Nizam704/Self-Guided-Projectile-Bot/Project parts/Solidworks parts/Part3.SLDPRT

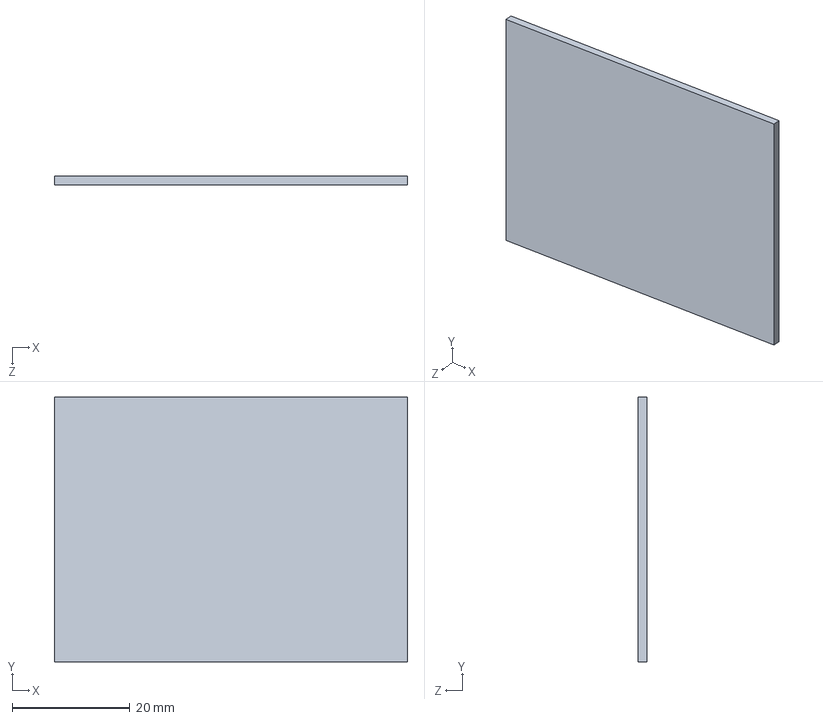
[picture p39: CAD file, 2025-05-20]
Project parts/Solidworks parts/Part3.SLDPRT
60.0 x 45.0 x 1.50 mm
