Nizam704/Self-Guided-Projectile-Bot/Project parts/Cura files/stand holder.STL

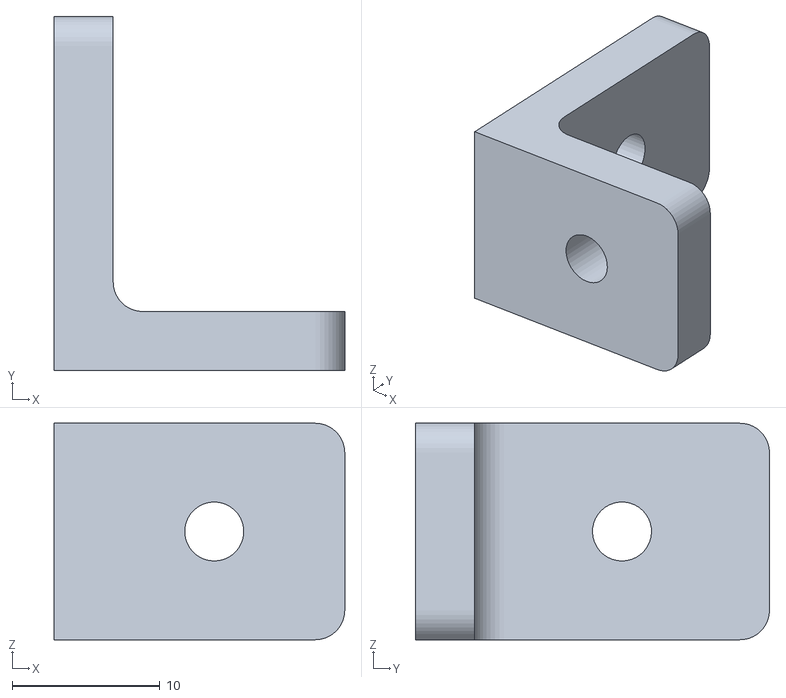
[picture p40: CAD file, 2025-05-20]
Project parts/Cura files/stand holder.STL
19.7 x 24.0 x 14.7
