Nizam704/Self-Guided-Projectile-Bot/Project parts/Cura files/ball holder preview.STL

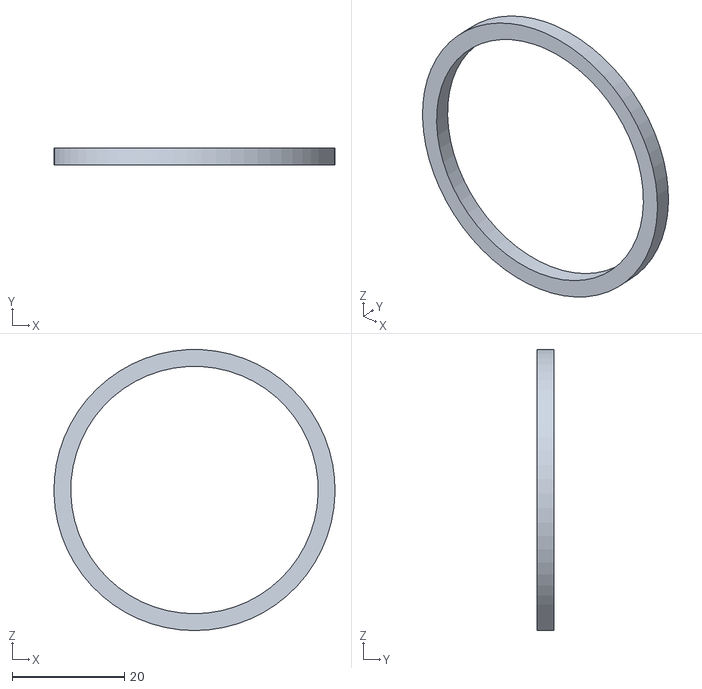
[picture p41: CAD file, 2025-05-20]
Project parts/Cura files/ball holder preview.STL
50.0 x 3.00 x 50.0
