Nizam704/Self-Guided-Projectile-Bot/Project parts/Solidworks parts/stand2.SLDPRT

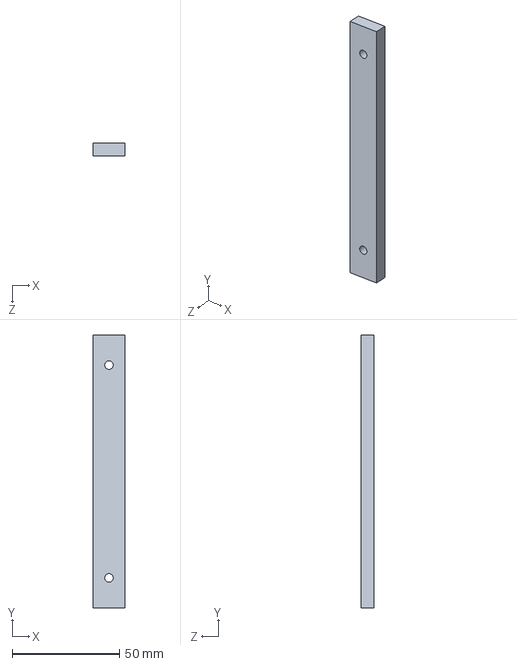
[picture p42: CAD file, 2025-05-20]
Project parts/Solidworks parts/stand2.SLDPRT
14.7 x 127.0 x 6.00 mm
