Nizam704/Self-Guided-Projectile-Bot/Project parts/Cura files/wheel.stl

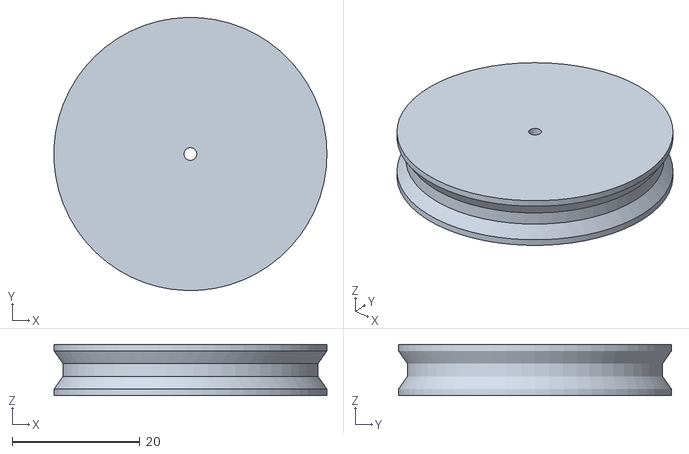
[picture p43: CAD file, 2025-05-20]
Project parts/Cura files/wheel.stl
42.8 x 42.8 x 8.00
