Nizam704/Self-Guided-Projectile-Bot/Project parts/Solidworks parts/Large Sides.SLDPRT

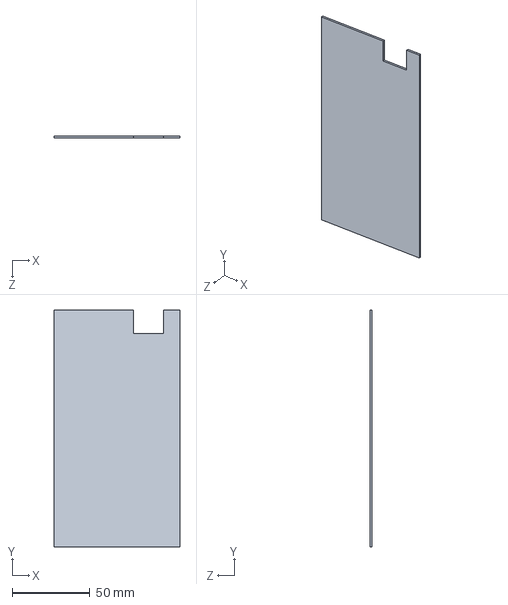
[picture p44: CAD file, 2025-05-20]
Project parts/Solidworks parts/Large Sides.SLDPRT
81.0 x 152.4 x 1.50 mm
