Nizam704/Self-Guided-Projectile-Bot/Project parts/Cura files/sensor base.STL

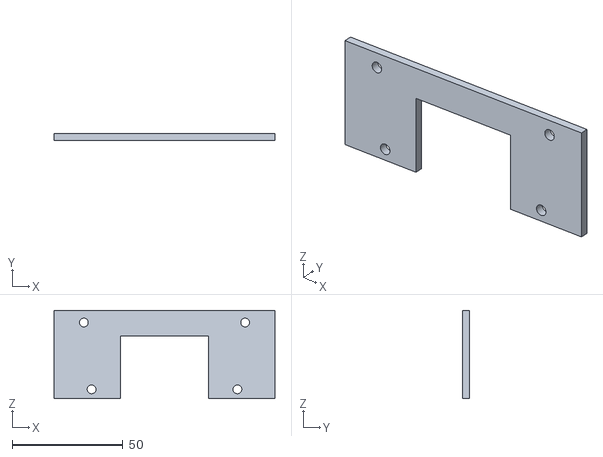
[picture p45: CAD file, 2025-05-20]
Project parts/Cura files/sensor base.STL
100.0 x 3.00 x 40.0
