Nizam704/Self-Guided-Projectile-Bot/Project parts/Solidworks parts/Lower Sides 2 (two parts).SLDPRT

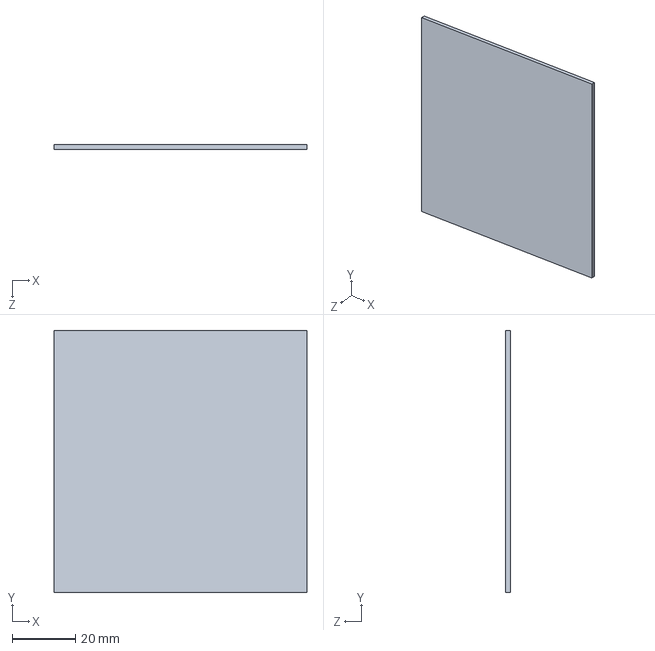
[picture p46: CAD file, 2025-05-20]
Project parts/Solidworks parts/Lower Sides 2 (two parts).SLDPRT
80.0 x 82.9 x 1.50 mm
