Nizam704/Self-Guided-Projectile-Bot/Project parts/Cura files/ball holder preview.SLDPRT.STL

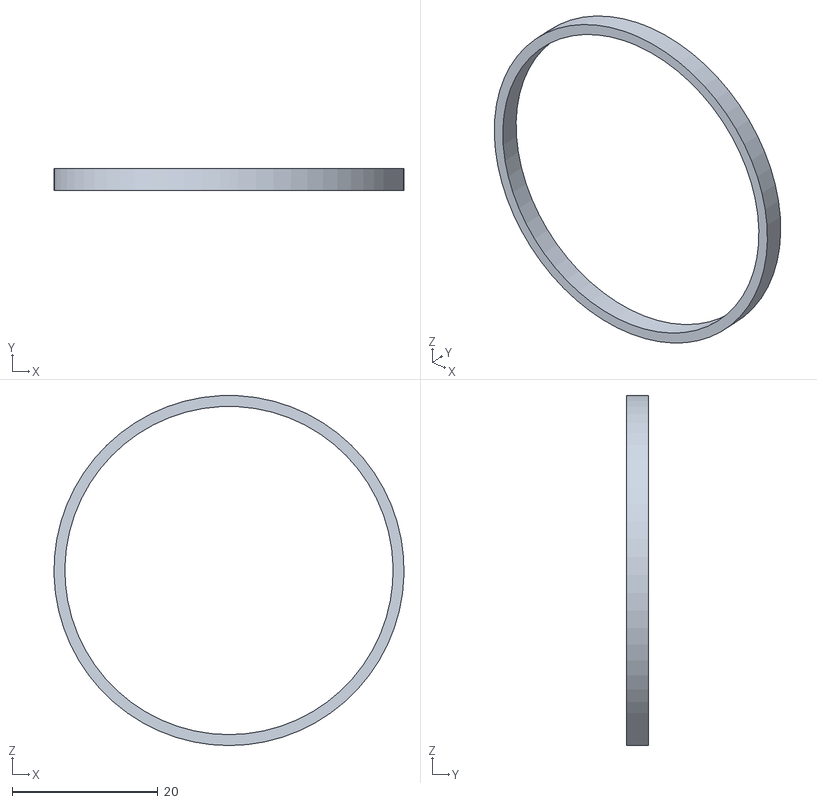
[picture p47: CAD file, 2025-05-20]
Project parts/Cura files/ball holder preview.SLDPRT.STL
48.0 x 3.00 x 48.0
