Nizam704/Self-Guided-Projectile-Bot/Project parts/Solidworks parts/Part2.SLDPRT

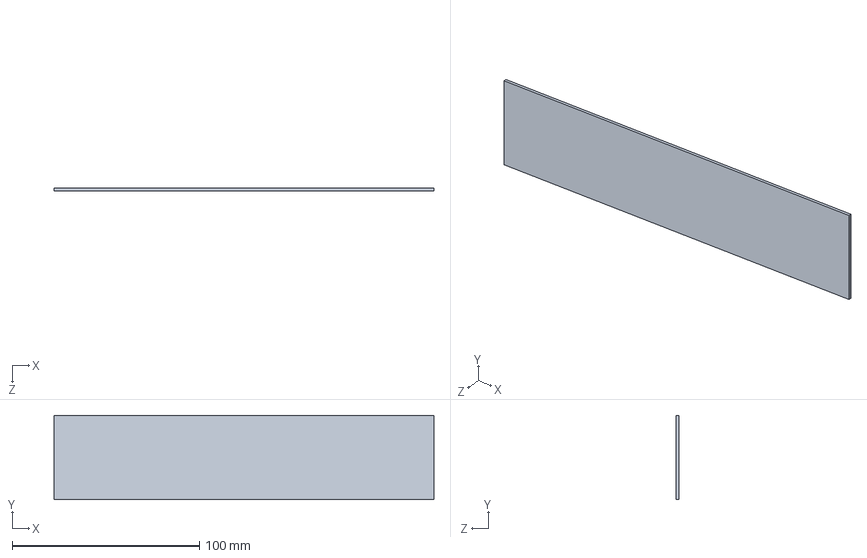
[picture p48: CAD file, 2025-05-20]
Project parts/Solidworks parts/Part2.SLDPRT
203.2 x 45.0 x 1.50 mm
