Nizam704/Self-Guided-Projectile-Bot/Project parts/Cura files/nameplate.STL

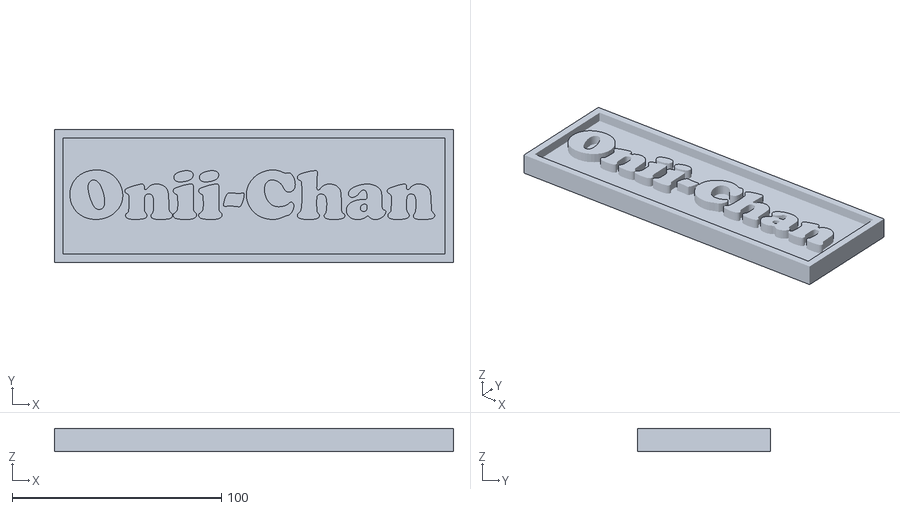
[picture p49: CAD file, 2025-05-20]
Project parts/Cura files/nameplate.STL
190.5 x 63.5 x 11.0
