Nizam704/Self-Guided-Projectile-Bot/Project parts/Solidworks parts/battery hold.SLDPRT

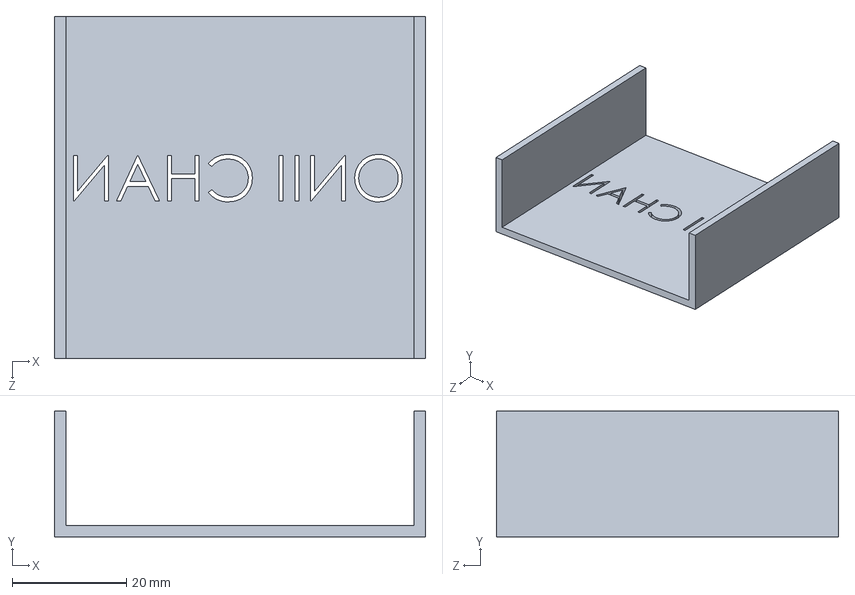
[picture p50: CAD file, 2025-05-20]
Project parts/Solidworks parts/battery hold.SLDPRT
65.0 x 22.0 x 60.0 mm
