Nizam704/Self-Guided-Projectile-Bot/Project parts/Cura files/ball holder ver 2.STL

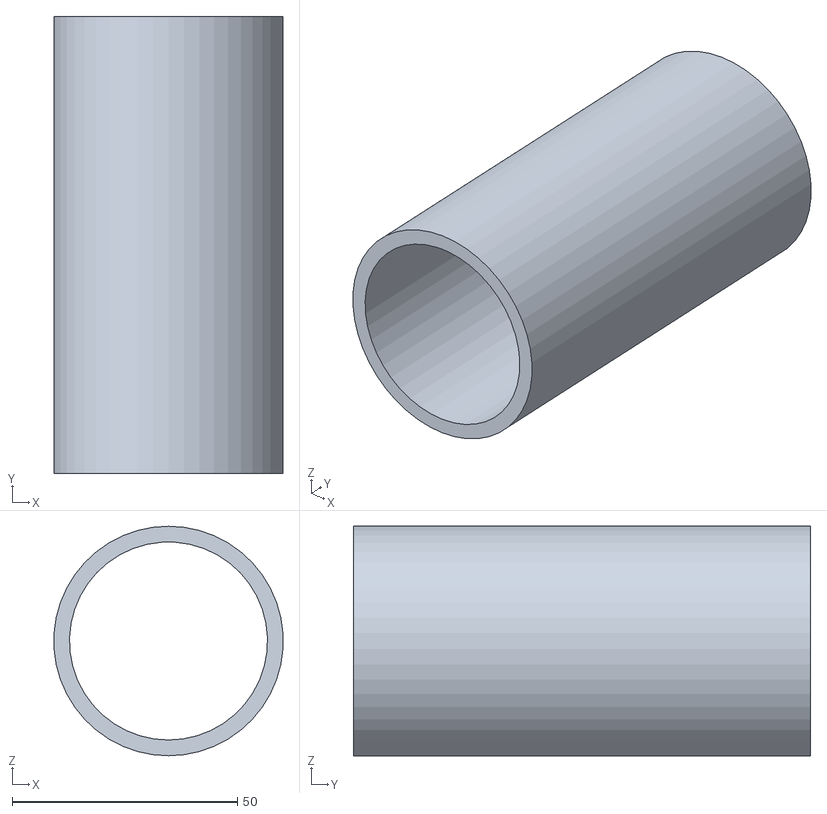
[picture p51: CAD file, 2025-05-20]
Project parts/Cura files/ball holder ver 2.STL
50.9 x 101.6 x 51.0
