Nizam704/Self-Guided-Projectile-Bot/Project parts/Solidworks parts/angle cone3.SLDPRT

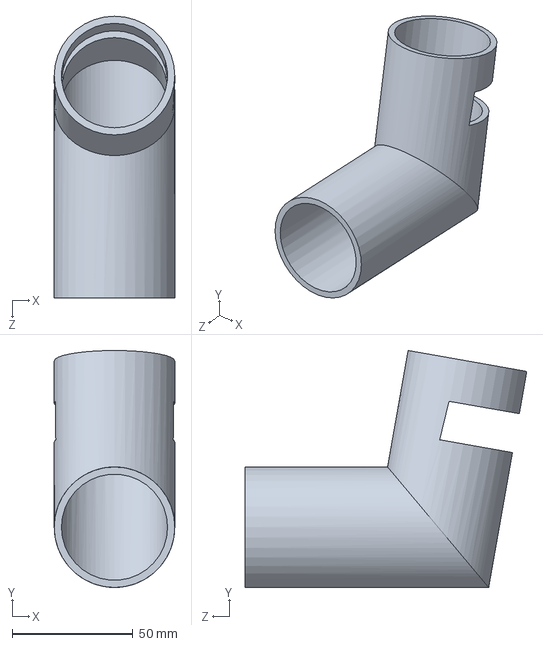
[picture p52: CAD file, 2025-05-20]
Project parts/Solidworks parts/angle cone3.SLDPRT
50.0 x 98.3 x 116.8 mm
