Nizam704/Self-Guided-Projectile-Bot/Project parts/Solidworks parts/Chassis Base 2.SLDPRT

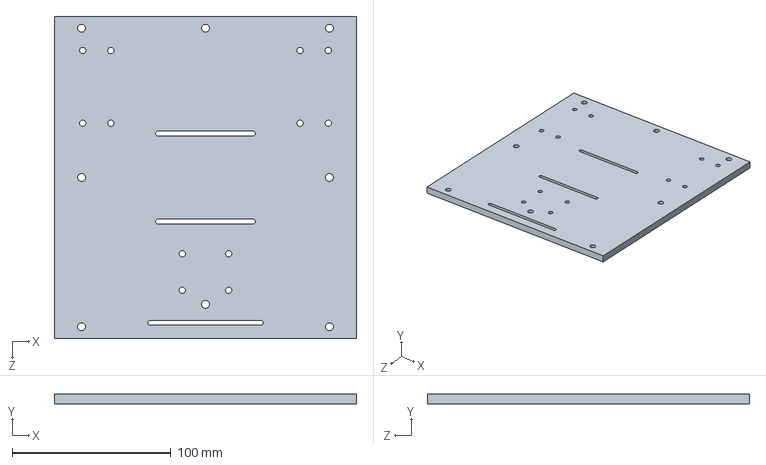
[picture p53: CAD file, 2025-05-20]
Project parts/Solidworks parts/Chassis Base 2.SLDPRT
190.5 x 6.00 x 203.2 mm
