Nizam704/Self-Guided-Projectile-Bot/Project parts/Solidworks parts/Upper Back.SLDPRT

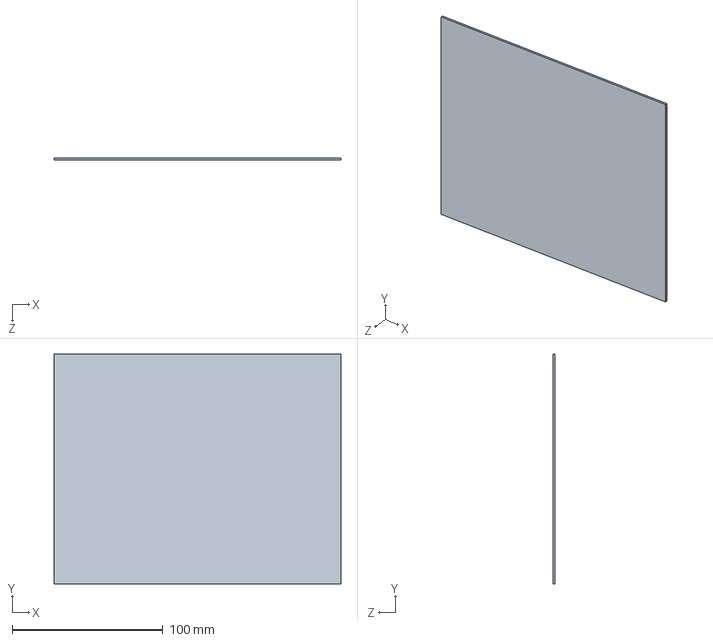
[picture p54: CAD file, 2025-05-20]
Project parts/Solidworks parts/Upper Back.SLDPRT
190.5 x 152.4 x 1.50 mm
