Nizam704/Self-Guided-Projectile-Bot/Project parts/Solidworks parts/Onii_chan.SLDPRT

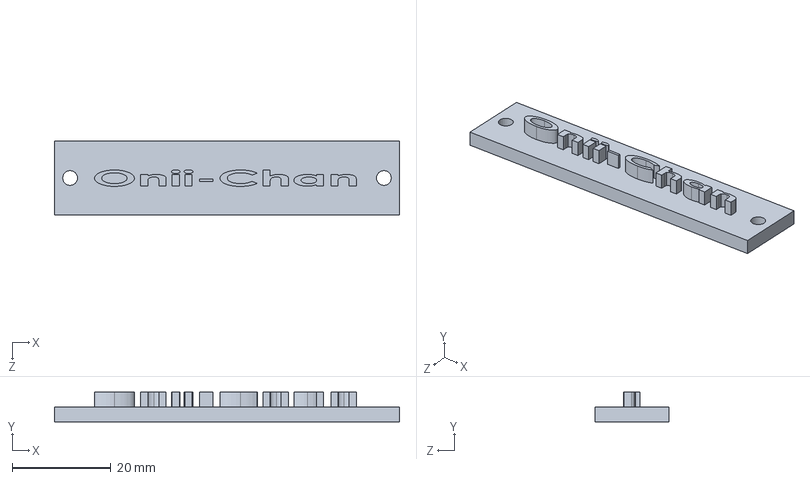
[picture p55: CAD file, 2025-05-20]
Project parts/Solidworks parts/Onii_chan.SLDPRT
70.0 x 6.00 x 15.0 mm
