Nizam704/Self-Guided-Projectile-Bot/Project parts/Solidworks parts/upper base.SLDPRT

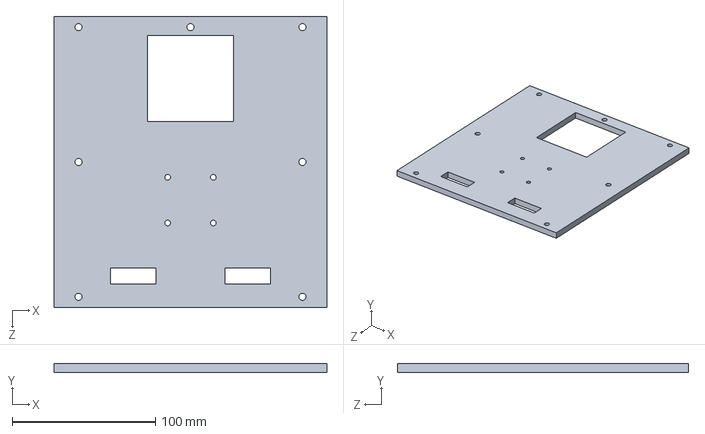
[picture p56: CAD file, 2025-05-20]
Project parts/Solidworks parts/upper base.SLDPRT
190.5 x 6.00 x 203.2 mm
