Nizam704/Self-Guided-Projectile-Bot/Project parts/Solidworks parts/stand.SLDPRT

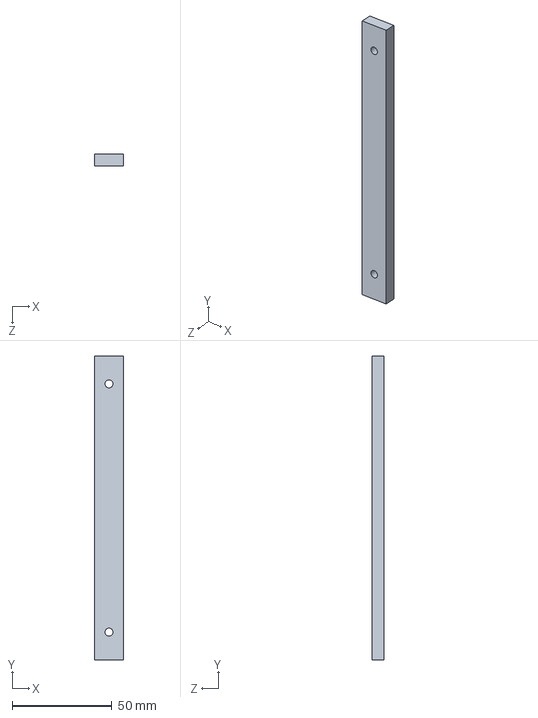
[picture p57: CAD file, 2025-05-20]
Project parts/Solidworks parts/stand.SLDPRT
14.7 x 152.4 x 6.00 mm
