Nizam704/Self-Guided-Projectile-Bot/Project parts/Solidworks parts/Part1.SLDPRT

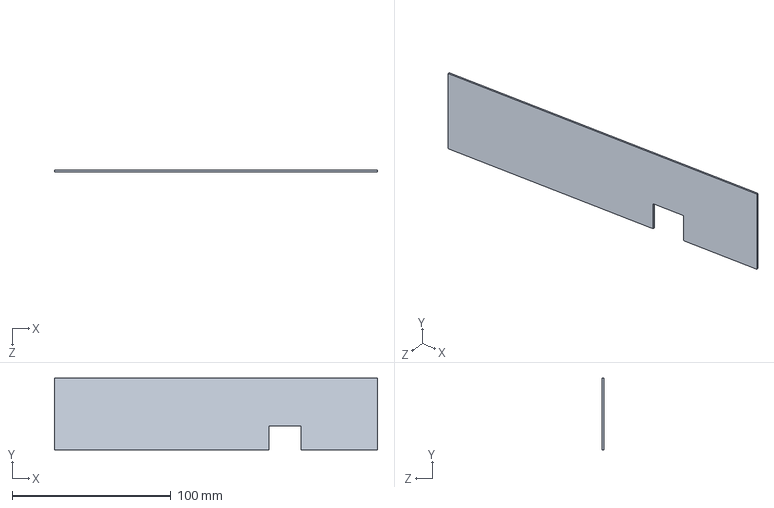
[picture p58: CAD file, 2025-05-20]
Project parts/Solidworks parts/Part1.SLDPRT
203.2 x 45.0 x 1.00 mm
