Nizam704/Self-Guided-Projectile-Bot/Project parts/Solidworks parts/ball holder ver 2.SLDPRT

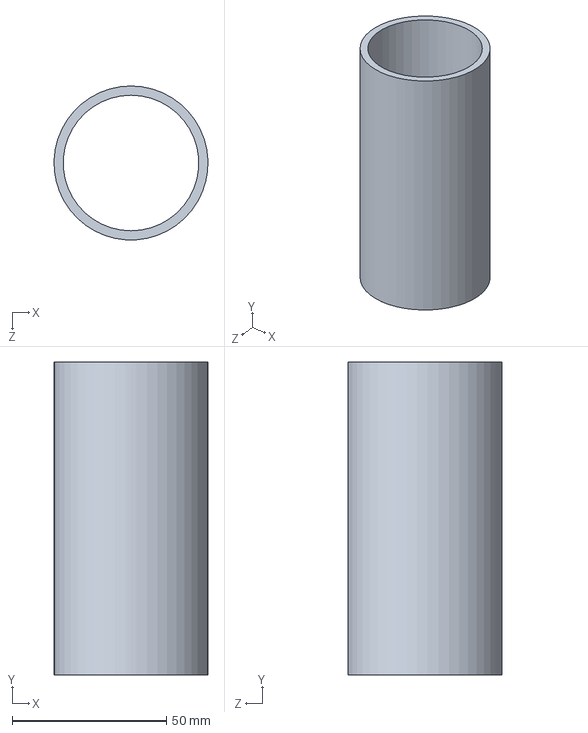
[picture p59: CAD file, 2025-05-20]
Project parts/Solidworks parts/ball holder ver 2.SLDPRT
50.0 x 101.6 x 50.0 mm
