Nizam704/Self-Guided-Projectile-Bot/Project parts/Solidworks parts/Part5.SLDPRT

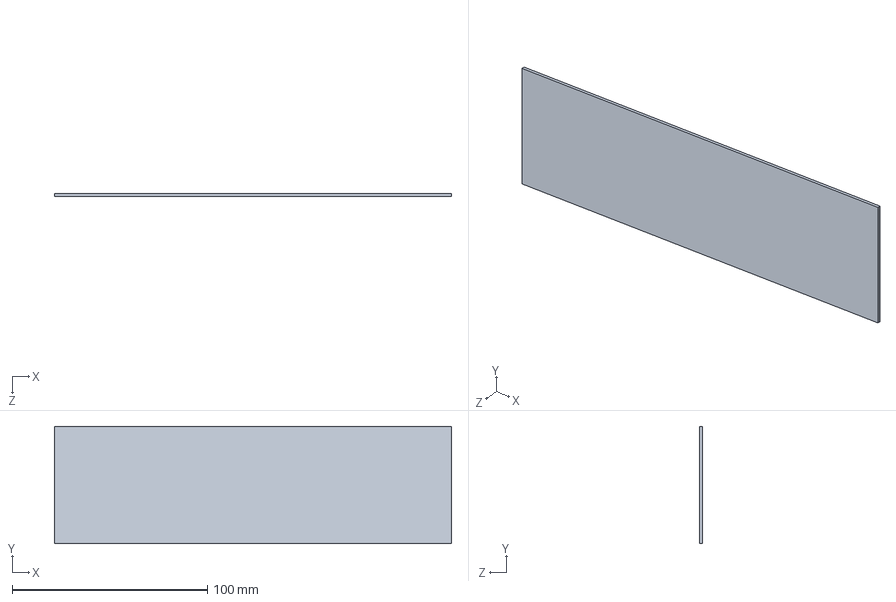
[picture p60: CAD file, 2025-05-20]
Project parts/Solidworks parts/Part5.SLDPRT
203.2 x 60.0 x 1.50 mm
